hazarkarabay/avr-tqfp-programmer/EASYEDA/Pictures/20201003_122340.jpg

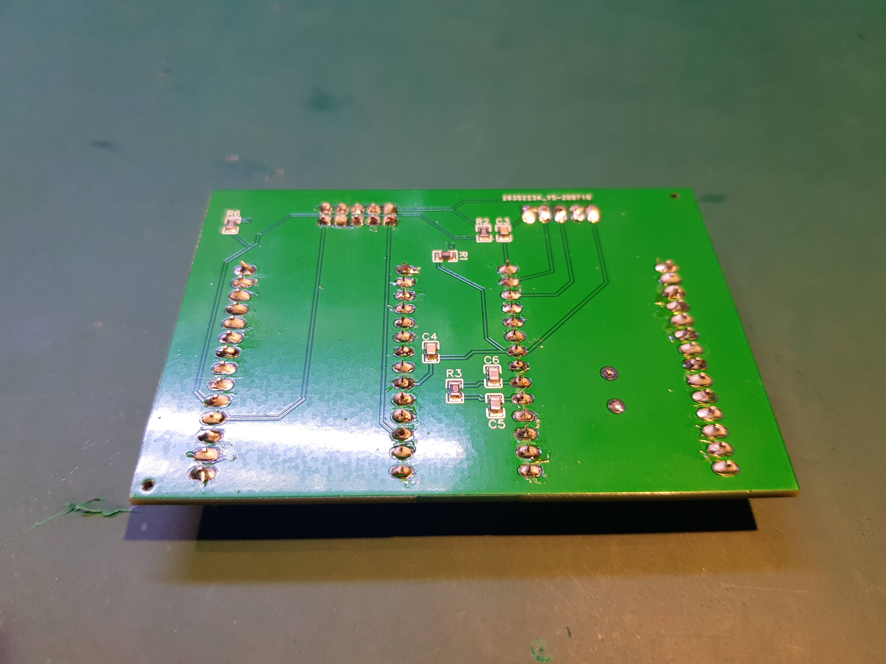
EASYEDA/Pictures/20201003_122340.jpg
