hazarkarabay/avr-tqfp-programmer/EASYEDA/Pictures/20201003_122443.jpg

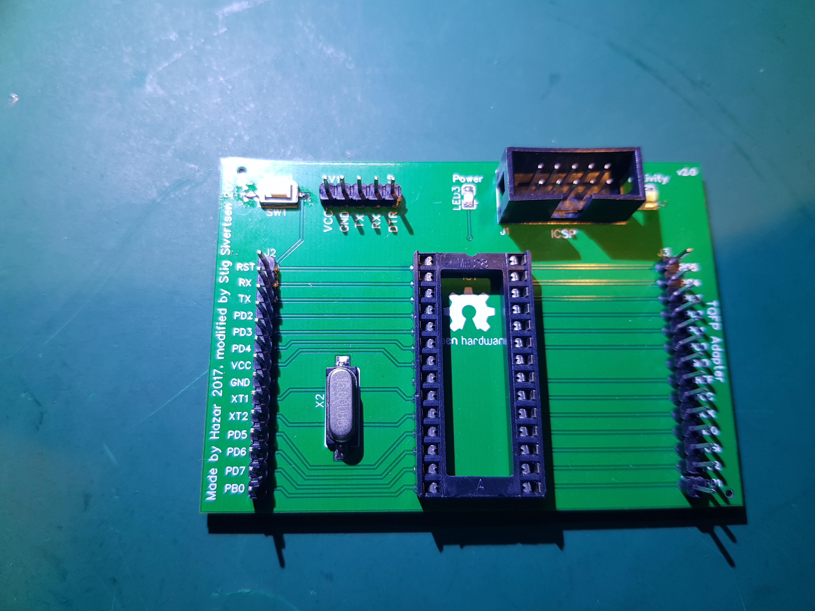
EASYEDA/Pictures/20201003_122443.jpg
