hazarkarabay/avr-tqfp-programmer/EASYEDA/Pictures/20201003_122506.jpg

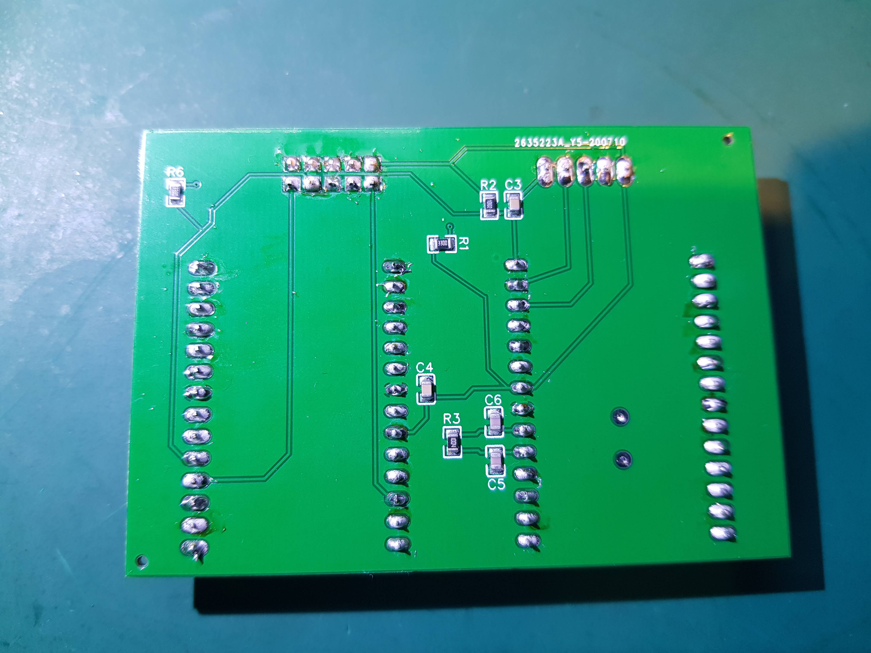
EASYEDA/Pictures/20201003_122506.jpg
