hazarkarabay/avr-tqfp-programmer/EASYEDA/Pictures/20201003_122532.jpg

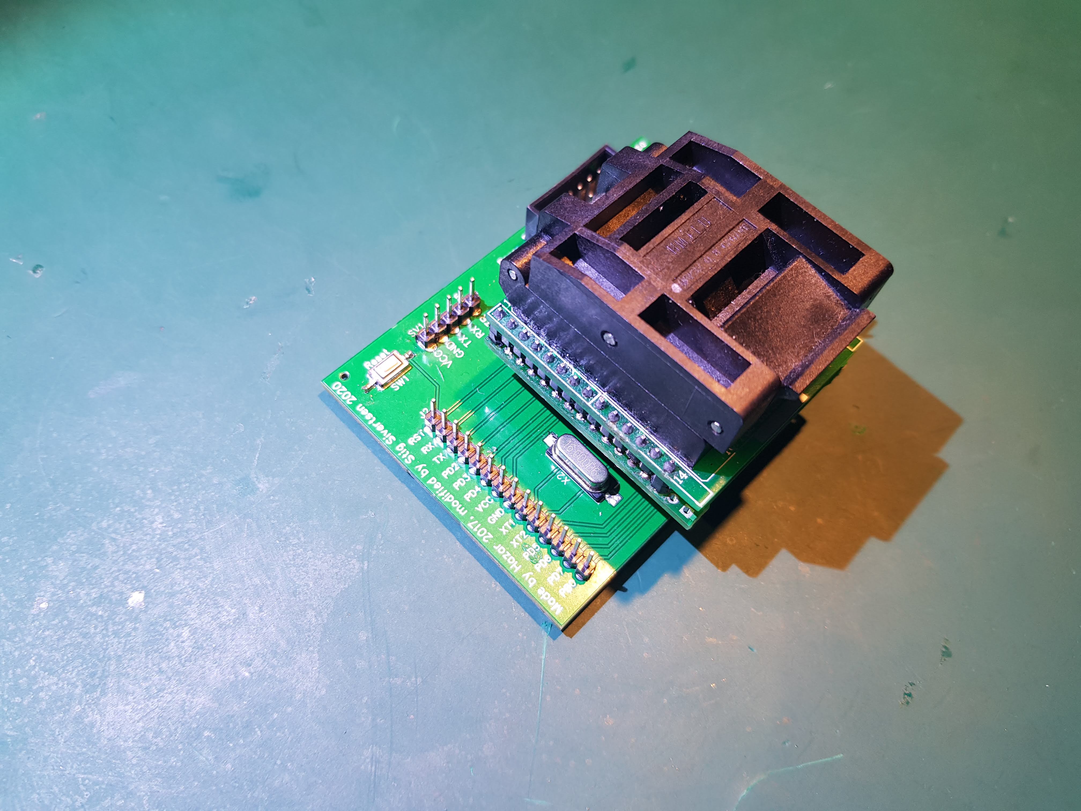
EASYEDA/Pictures/20201003_122532.jpg
