hazarkarabay/avr-tqfp-programmer/EASYEDA/Pictures/20201003_122543.jpg

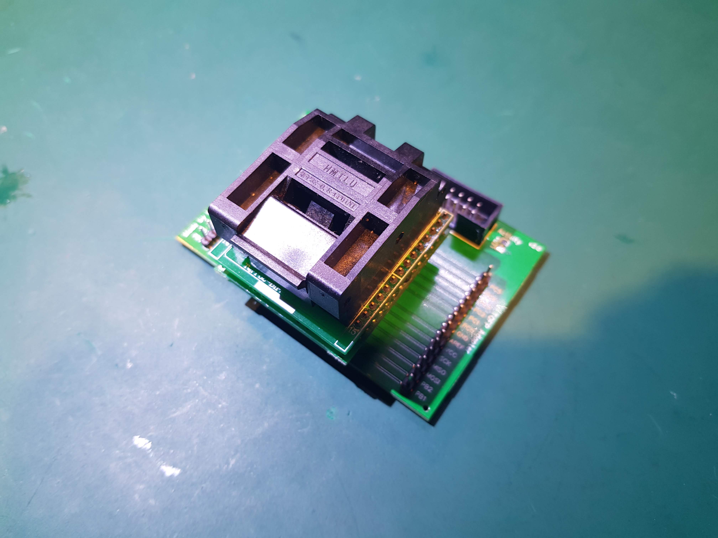
EASYEDA/Pictures/20201003_122543.jpg
