hazarkarabay/avr-tqfp-programmer/EASYEDA/Pictures/20201003_122650.jpg

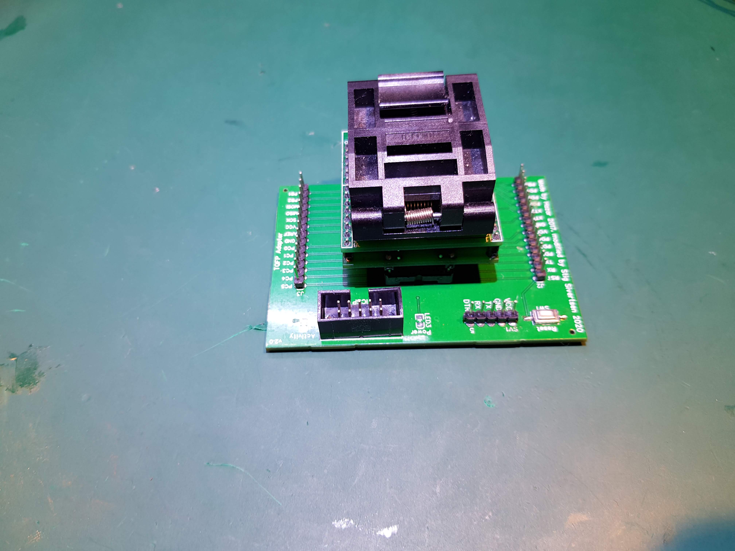
EASYEDA/Pictures/20201003_122650.jpg
