hazarkarabay/avr-tqfp-programmer/EASYEDA/Pictures/20201003_122734.jpg

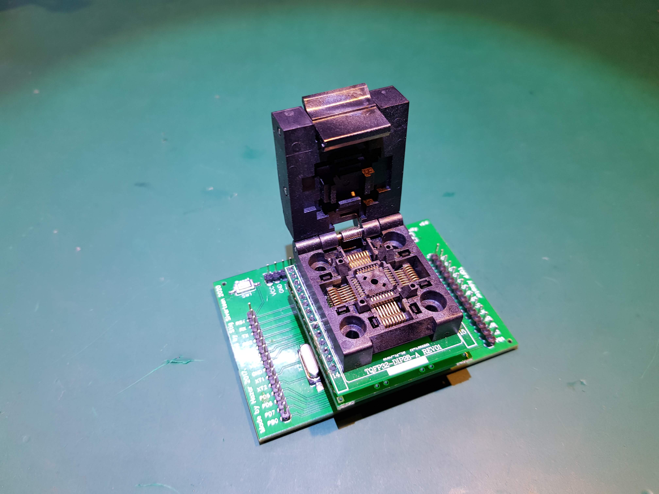
EASYEDA/Pictures/20201003_122734.jpg
