hazarkarabay/avr-tqfp-programmer/EASYEDA/Pictures/20201003_122738.jpg

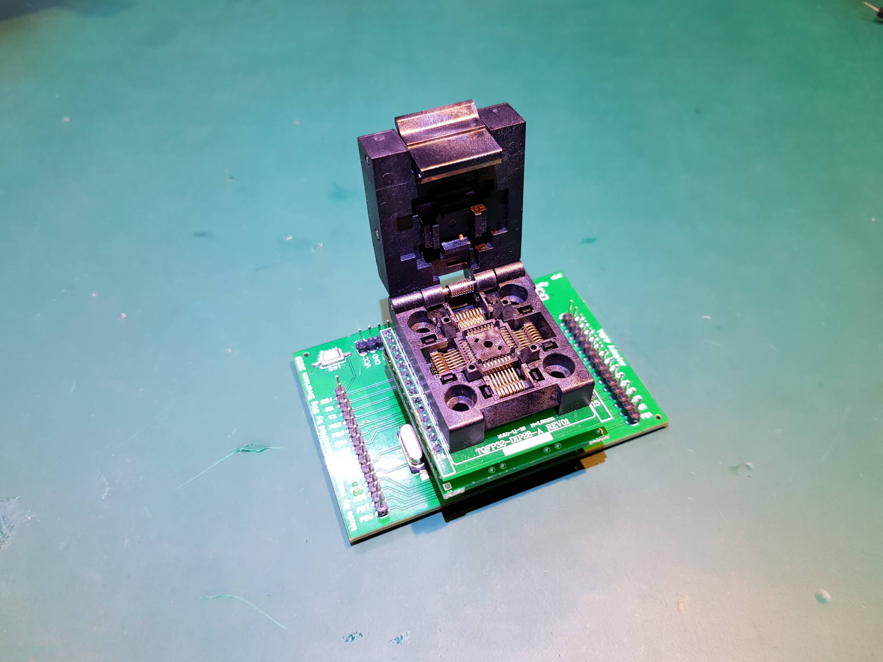
EASYEDA/Pictures/20201003_122738.jpg
